ikok07/esp32-light-switch/main/include/light_control.h

//
// Created by Kok on 3/9/26.
//

#ifndef ESP32S3_BLE_RELAY_H
#define ESP32S3_BLE_RELAY_H

#define LIGHT_CTRL_GPIO                         GPIO_NUM_17
#define LIGHT_TOGGLE_GPIO                       GPIO_NUM_21

void LCTRL_Init();

#endif //ESP32S3_BLE_RELAY_H
