ikok07/esp32-light-switch/main/bt-config.c

//
// Created by Kok on 3/10/26.
//

#include <status_led.h>
#include <string.h>

#include "bt-config.h"
#include "ble.h"
#include "log.h"
#include "app_state.h"

#define BLE_DEVICE_PASSWORD                                             246300

static const ble_uuid128_t identifier_service_uuid = BLE_UUID128_INIT(
    0x88, 0xc8, 0x5b, 0xc1, 0xfe, 0xec, 0x4c, 0x35,
    0xaa, 0x49, 0x74, 0xae, 0x36, 0x35, 0x51, 0x65
);

static const ble_uuid16_t automation_service_uuid = BLE_UUID16_INIT(0x1815);

static const ble_uuid16_t digital_chr_uuid = BLE_UUID16_INIT(0x2A56);

static const ble_uuid16_t description_dsc_uuid = BLE_UUID16_INIT(0x2901);
static const ble_uuid16_t presentation_dsc_uuid = BLE_UUID16_INIT(0x2904);
static const ble_uuid16_t num_digitals_dsc_uuid = BLE_UUID16_INIT(0x2909);

#define BLE_DSC_OBJ_DESCRIPTION(AccessCB, Description)             {\
                                                                        .uuid = &description_dsc_uuid.u,\
                                                                        .att_flags = BLE_ATT_F_READ,\
                                                                        .access_cb = AccessCB,\
                                                                        .arg = Description\
                                                                    }\


BLE_AttributesTypeDef gBleAttributes;
ble_uuid128_t gAdvertised128Services[] = {identifier_service_uuid};

/* ------ Driver CBs ------ */

void on_gap_event(BLE_GapEventTypeDef Event, struct ble_gap_event *GapEvent, void *Arg);
void on_gatt_reg_event(BLE_GattRegisterEventTypeDef Event, struct ble_gatt_register_ctxt *EventCtxt, void *Arg);
uint8_t on_gatt_subscribe_event(struct ble_gap_event *event);
void on_error(BLE_ErrorTypeDef Error);
void on_advertise(struct ble_hs_adv_fields *Fields);

/* ------ Services Access CBs ------ */

int light_state_access_cb(uint16_t conn_handle, uint16_t attr_handle,
                          struct ble_gatt_access_ctxt *ctxt, void *arg);

int light_state_char_presentation_dsc_access_cb(uint16_t conn_handle, uint16_t attr_handle,
                               struct ble_gatt_access_ctxt *ctxt, void *arg);

int num_digitals_dsc_access_cb(uint16_t conn_handle, uint16_t attr_handle,
                               struct ble_gatt_access_ctxt *ctxt, void *arg);

int description_dsc_access_cb(uint16_t conn_handle, uint16_t attr_handle,
                               struct ble_gatt_access_ctxt *ctxt, void *arg);

static struct ble_gatt_svc_def gGattServices[] = {
    {
        // Used for identification of Home Assistant integration
        .type = BLE_GATT_SVC_TYPE_PRIMARY,
        .uuid = &identifier_service_uuid.u
    },
    {
        .type = BLE_GATT_SVC_TYPE_PRIMARY,
        .uuid = &automation_service_uuid.u,
        .characteristics = (struct ble_gatt_chr_def[]) {
                {
                    .uuid = &digital_chr_uuid.u,
                    .flags = BLE_GATT_CHR_F_READ | BLE_GATT_CHR_F_WRITE | BLE_GATT_CHR_F_NOTIFY,
                    .val_handle = &gBleAttributes.LightStateChrHandle,
                    .access_cb = light_state_access_cb,
                    .descriptors = (struct ble_gatt_dsc_def[]){
                        {
                            .uuid = &presentation_dsc_uuid.u,
                            .att_flags = BLE_ATT_F_READ,
                            .access_cb = light_state_char_presentation_dsc_access_cb
                        },
                        {
                            .uuid = &num_digitals_dsc_uuid.u,
                            .att_flags = BLE_ATT_F_READ,
                            .access_cb = num_digitals_dsc_access_cb
                        },
                            BLE_DSC_OBJ_DESCRIPTION(description_dsc_access_cb, "Light state"),
                        {0}
                    }
                },
            {0}
        },
    },
    {0}
};

void BT_Configure(BLE_HandleTypeDef *hble) {
    hble->Callbacks = (BLE_CallbacksTypeDef) {
        .on_gap_event = on_gap_event,
        .on_gatt_reg_event = on_gatt_reg_event,
        .on_gatt_subscribe_event = on_gatt_subscribe_event,
        .on_advertise = on_advertise,
        .on_error = on_error
    };

    hble->Config.GattServices = gGattServices;
}

void on_gap_event(BLE_GapEventTypeDef Event, struct ble_gap_event *GapEvent, void *Arg) {
    switch (Event) {
        case BLE_GAP_EVENT_CONN_SUCCESS:
            LOGGER_LogF(LOGGER_LEVEL_INFO, "BLE Device %d connected!", GapEvent->connect.conn_handle);
            STATUSLED_SetState(STATUSLED_STATE_CONNECTED);
            break;
        case BLE_GAP_EVENT_CONN_FAILED:
            LOGGER_Log(LOGGER_LEVEL_INFO, "BLE Device connection failed!");
            break;
        case BLE_GAP_EVENT_CONN_STORE_FAILED:
            LOGGER_LogF(LOGGER_LEVEL_INFO, "BLE Device %d connection store failed!", GapEvent->connect.conn_handle);
            break;
        case BLE_GAP_EVENT_CONN_UPD:
            LOGGER_LogF(LOGGER_LEVEL_INFO, "BLE Device %d connection updated!", GapEvent->conn_update.conn_handle);
            break;
        case BLE_GAP_EVENT_CONN_DISCONNECT:
            LOGGER_LogF(LOGGER_LEVEL_INFO, "BLE Device %d disconnected!", GapEvent->disconnect.conn.conn_handle);
            if (!BLE_CheckConnectionsAvailable(gAppState.hble)) STATUSLED_SetState(STATUSLED_STATE_READY_TO_CONNECT);
            break;
        case BLE_GAP_EVENT_SUB:
            LOGGER_LogF(LOGGER_LEVEL_INFO, "BLE Device %d subscribed!", GapEvent->subscribe.conn_handle);
            break;
        case BLE_GAP_EVENT_CONN_ENC:
            LOGGER_Log(LOGGER_LEVEL_INFO, "BLE Connection encrypted");
            break;
        case BLE_GAP_EVENT_CONN_ENC_FAILED:
            LOGGER_LogF(LOGGER_LEVEL_ERROR, "BLE Connection could not be encrypted! Status code: %d", GapEvent->enc_change.status);
            break;
        case BLE_GAP_EVENT_UNSUB:
            LOGGER_LogF(LOGGER_LEVEL_INFO, "BLE Device %d unsubscribed!", GapEvent->subscribe.conn_handle);
            break;
        case BLE_GAP_EVENT_PASSKEY:
            if (GapEvent->passkey.params.action == BLE_SM_IOACT_DISP) {
                struct ble_sm_io pkey= {0};
                pkey.action = GapEvent->passkey.params.action;
                pkey.passkey = BLE_DEVICE_PASSWORD;
                ble_sm_inject_io(GapEvent->passkey.conn_handle, &pkey);
            }
            break;
        default:
            LOGGER_LogF(LOGGER_LEVEL_WARNING, "Unhandled GAP event %d!", Event);
            break;
    }
}

void on_gatt_reg_event(BLE_GattRegisterEventTypeDef Event, struct ble_gatt_register_ctxt *EventCtxt, void *Arg) {
    switch (Event) {
        case BLE_GATT_REG_EVENT_REG_SVC:
            LOGGER_LogF(LOGGER_LEVEL_INFO, "New service registered! Handle: 0x%04X", EventCtxt->svc.handle);
            break;
        case BLE_GATT_REG_EVENT_REG_CHR:
            LOGGER_LogF(LOGGER_LEVEL_INFO, "New service characteristic registered! Handle: 0x%04X", EventCtxt->svc.handle);
            break;
        case BLE_GATT_REG_EVENT_REG_DSC:
            LOGGER_LogF(LOGGER_LEVEL_INFO, "New characteristic descriptor registered! Handle: 0x%04X", EventCtxt->svc.handle);
            break;
        default:
            break;
    }
}

uint8_t on_gatt_subscribe_event(struct ble_gap_event *event) {
    if (event->subscribe.attr_handle == gBleAttributes.LightStateChrHandle) {
        uint8_t is_encrypted;
        if (BLE_CheckConnEncrypted(event->subscribe.conn_handle, &is_encrypted) != BLE_ERROR_OK || !is_encrypted) {
            return BLE_ATT_ERR_INSUFFICIENT_AUTHEN;
        }
    }
    return 0;
}

void on_error(BLE_ErrorTypeDef Error) {
    LOGGER_LogF(LOGGER_LEVEL_ERROR, "An error occurred in BLE driver! Error code: %d", Error);
}

void on_advertise(struct ble_hs_adv_fields *Fields) {
    Fields->uuids128 = gAdvertised128Services;
    Fields->num_uuids128 = 1;
    Fields->uuids128_is_complete = 1;
}

int light_state_access_cb(uint16_t conn_handle, uint16_t attr_handle,
                        struct ble_gatt_access_ctxt *ctxt, void *arg) {
    uint8_t err = 0;
    SHVAL_ErrorTypeDef shval_err;

    switch (ctxt->op) {
        case BLE_GATT_ACCESS_OP_READ_CHR:
            uint32_t light_state;
            if ((shval_err = SHVAL_GetValue(&gAppState.SharedValues->LightState, &light_state, 1000)) != SHVAL_ERROR_OK) {
                LOGGER_LogF(LOGGER_LEVEL_ERROR, "Failed to get shared LED light state! Error code: %d", shval_err);
                return BLE_ATT_ERR_UNLIKELY;
            }

            err = os_mbuf_append(ctxt->om, &light_state, 1);

            return err == 0 ? 0 : BLE_ATT_ERR_INSUFFICIENT_RES;
        case BLE_GATT_ACCESS_OP_WRITE_CHR:
            if (ctxt->om->om_len != 1) return BLE_ATT_ERR_VALUE_NOT_ALLOWED;
            uint8_t write_val = *ctxt->om->om_data;
            if (write_val > 1) return BLE_ATT_ERR_VALUE_NOT_ALLOWED;

            xTaskNotify(gAppState.Tasks->LightCtrlTask.OsTask, write_val, eSetValueWithOverwrite);
            return 0;
        default:
            break;
    }

    return BLE_ATT_ERR_UNLIKELY;
}

int light_state_char_presentation_dsc_access_cb(uint16_t conn_handle, uint16_t attr_handle,
    struct ble_gatt_access_ctxt *ctxt, void *arg) {
    uint8_t format = 0x01;                  // Boolean
    return os_mbuf_append(ctxt->om, &format, 1);
}

int num_digitals_dsc_access_cb(uint16_t conn_handle, uint16_t attr_handle, struct ble_gatt_access_ctxt *ctxt,
    void *arg) {
    uint8_t count = 1;
    return os_mbuf_append(ctxt->om, &count, 1);
}

int description_dsc_access_cb(uint16_t conn_handle, uint16_t attr_handle,
                              struct ble_gatt_access_ctxt *ctxt, void *arg) {
    if (ctxt->op != BLE_GATT_ACCESS_OP_READ_DSC) return BLE_ATT_ERR_UNLIKELY;
    const char *name = (const char*)arg;
    return os_mbuf_append(ctxt->om, name, strlen(name));
}
