ikok07/esp32-light-switch/main/include/bt.h

//
// Created by Kok on 2/14/26.
//

#ifndef ESP32S3_BLE_BT_H
#define ESP32S3_BLE_BT_H

#include "ble.h"

#define BT_MANUFACTURER_NAME                                    "Kaloyan Stefanov"
#define BT_SERIAL                                               "LS001"
#define BT_DEVICE_TYPE                                          0x50

void BT_Init();

#endif //ESP32S3_BLE_BT_H
