ikok07/esp32-light-switch/main/include/bt-config.h

//
// Created by Kok on 3/10/26.
//

#ifndef ESP32S3_BLE_BLE_CONFIG_H
#define ESP32S3_BLE_BLE_CONFIG_H

#include "ble.h"

typedef struct {
    uint16_t LightStateChrHandle;
} BLE_AttributesTypeDef;

extern BLE_AttributesTypeDef gBleAttributes;

void BT_Configure(BLE_HandleTypeDef *hble);

#endif //ESP32S3_BLE_BLE_CONFIG_H
