ikok07/esp32-light-switch/main/include/tasks_common.h

//
// Created by Kok on 2/12/26.
//

#ifndef ESP32S3_TASKS_COMMON_H
#define ESP32S3_TASKS_COMMON_H

/* ------ CORE 0 ------ */

#define BLE_TASK_CORE_ID                            0
#define BLE_TASK_STACK_DEPTH                        4096
#define BLE_TASK_PRIORITY                           5

#define BT_CFG_TASK_CORE_ID                         0
#define BT_CFG_TASK_STACK_DEPTH                     4096
#define BT_CFG_TASK_PRIORITY                        4

/* ------ CORE 1 ------ */

#define LIGHT_CONTROL_CFG_TASK_CORE_ID              1
#define LIGHT_CONTROL_CFG_TASK_STACK_DEPTH          4096
#define LIGHT_CONTROL_CFG_TASK_PRIORITY             5

#define LIGHT_CONTROL_TASK_CORE_ID                  1
#define LIGHT_CONTROL_TASK_STACK_DEPTH              4096
#define LIGHT_CONTROL_TASK_PRIORITY                 5

#define BLE_LIGHT_STATE_N_TASK_CORE_ID              1
#define BLE_LIGHT_STATE_N_TASK_STACK_DEPTH          4096
#define BLE_LIGHT_STATE_N_TASK_PRIORITY             5

#define STATUS_LED_CFG_TASK_CORE_ID                 1
#define STATUS_LED_CFG_TASK_STACK_DEPTH             2048
#define STATUS_LED_CFG_TASK_PRIORITY                4

#define STATUS_LED_TASK_CORE_ID                     1
#define STATUS_LED_TASK_STACK_DEPTH                 4096
#define STATUS_LED_TASK_PRIORITY                    4

#endif //ESP32S3_TASKS_COMMON_H
